UnexpectedMaker/manual_pnp_turntable/step/turntable_V3_rotation_plug.step

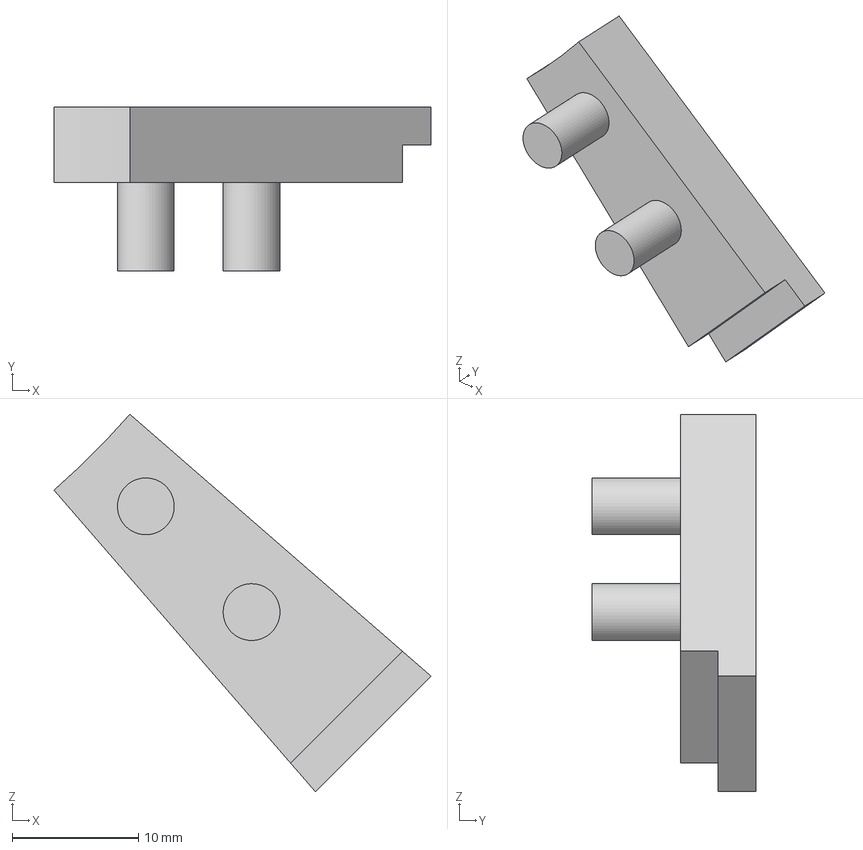
[picture p23: CAD file, 2021-02-13]
step/turntable_V3_rotation_plug.step
29.9 x 13.0 x 29.9 mm
