UnexpectedMaker/manual_pnp_turntable/openscad/turntable_parts_tray_partA.stl

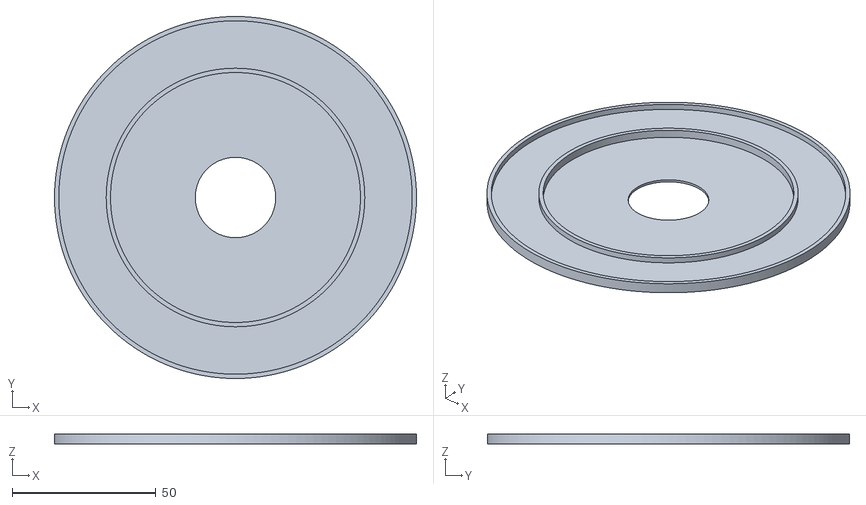
[picture p24: CAD file, 2021-04-20]
openscad/turntable_parts_tray_partA.stl
126.0 x 126.0 x 3.60
