UnexpectedMaker/manual_pnp_turntable/openscad/turntable_component_tray.scad

include <turntable.scad>

component_tray();
