UnexpectedMaker/manual_pnp_turntable/openscad/turntable_parts_tray_hole.scad

include <turntable.scad>

parts_tray(1,1);
