UnexpectedMaker/manual_pnp_turntable/openscad/turntable_parts_tray_partA.scad

include <turntable.scad>

parts_tray(0,2);
