UnexpectedMaker/manual_pnp_turntable/openscad/turntable_parts_tray_partB_nohole.scad

include <turntable.scad>

translate( [0,0,parts_thk/2] )
    rotate([180,0,0])
        parts_tray(0,3);
